tacitern/DigitalFadingLED/hardware/LedBoard/LedBoard.step

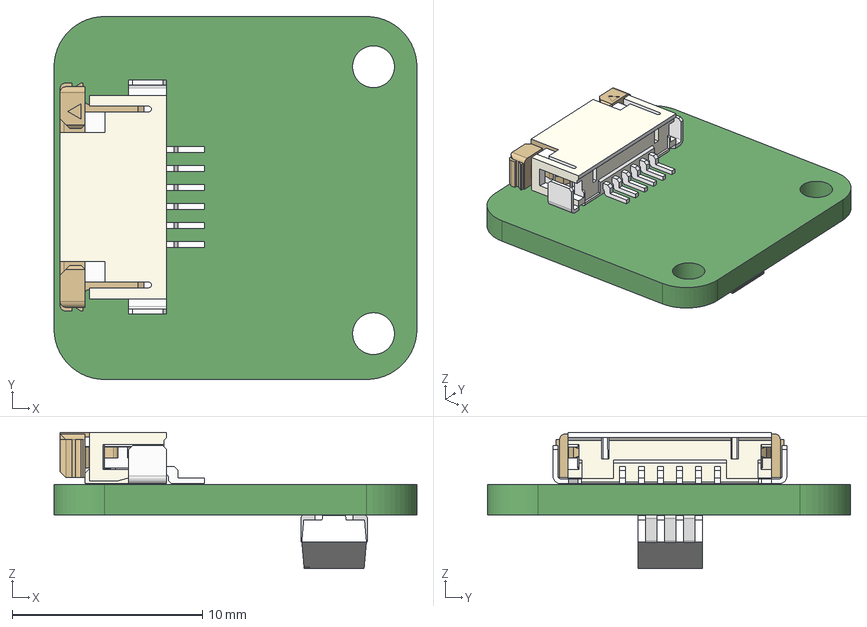
[picture p15: CAD file, 2021-11-26]
hardware/LedBoard/LedBoard.step
19.1 x 19.1 x 7.17 mm
