tacitern/DigitalFadingLED/hardware/ProgrammingAdapterBoard/footprints/Preci-Dip_851-87-007-20-001101_7pos_Soccket/851-87-007-20-001101.step

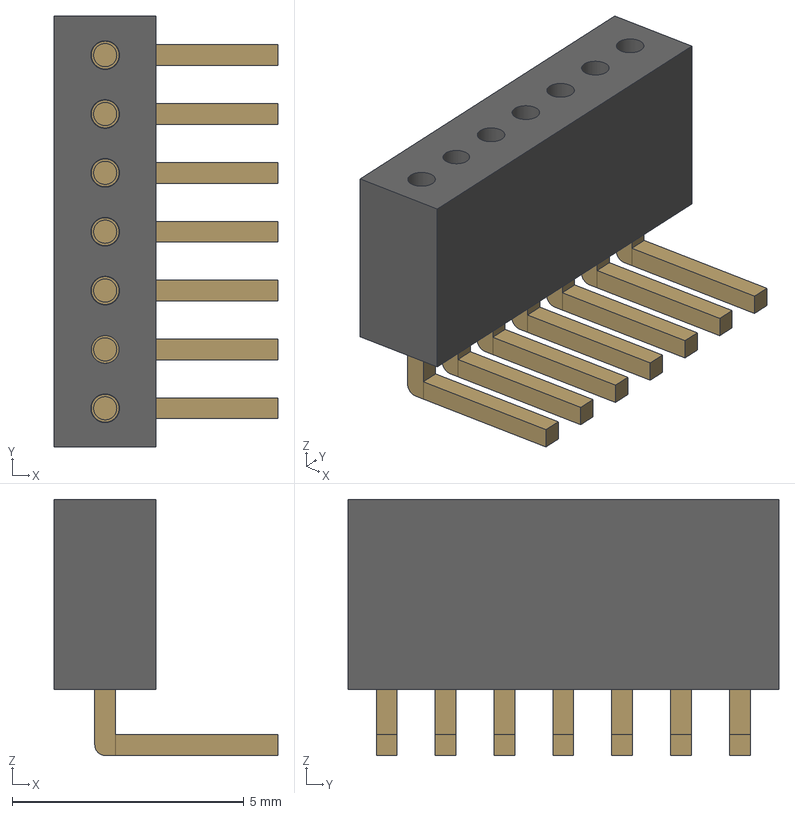
[picture p16: CAD file, 2021-11-26]
hardware/ProgrammingAdapterBoard/footprints/Preci-Dip_851-87-007-20-001101_7pos_Soccket/851-87-007-20-001101.step
4.83 x 9.30 x 5.52 mm
