tacitern/DigitalFadingLED/hardware/ProgrammingAdapterBoard/ProgrammingAdapterBoard.step

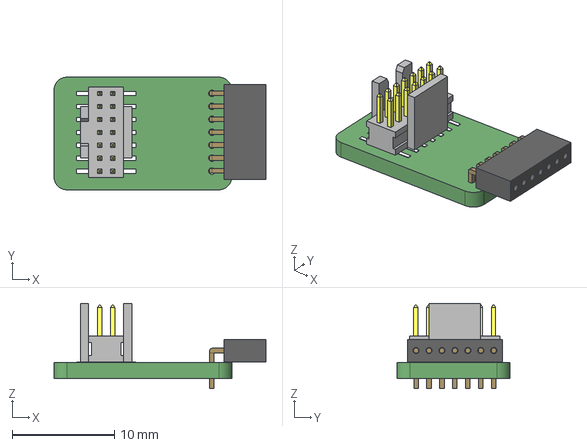
[picture p17: CAD file, 2021-11-26]
hardware/ProgrammingAdapterBoard/ProgrammingAdapterBoard.step
20.8 x 11.0 x 8.34 mm
