tacitern/DigitalFadingLED/hardware/DigitalFadingLED/footprints/FT230XS/FX230XS.FCStd

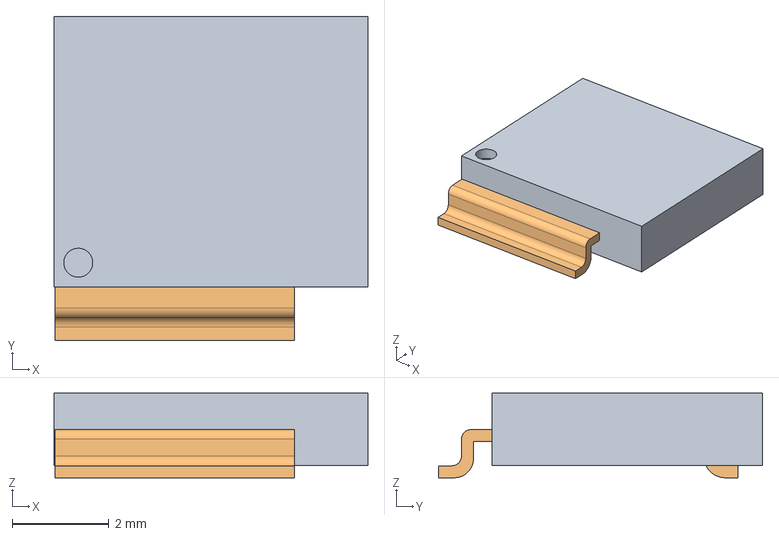
[picture p18: CAD file, 2021-11-26]
hardware/DigitalFadingLED/footprints/FT230XS/FX230XS.FCStd
6.50 x 6.71 x 1.75 mm
