tacitern/DigitalFadingLED/hardware/LedBoard/footprints/PLCC6.FCStd

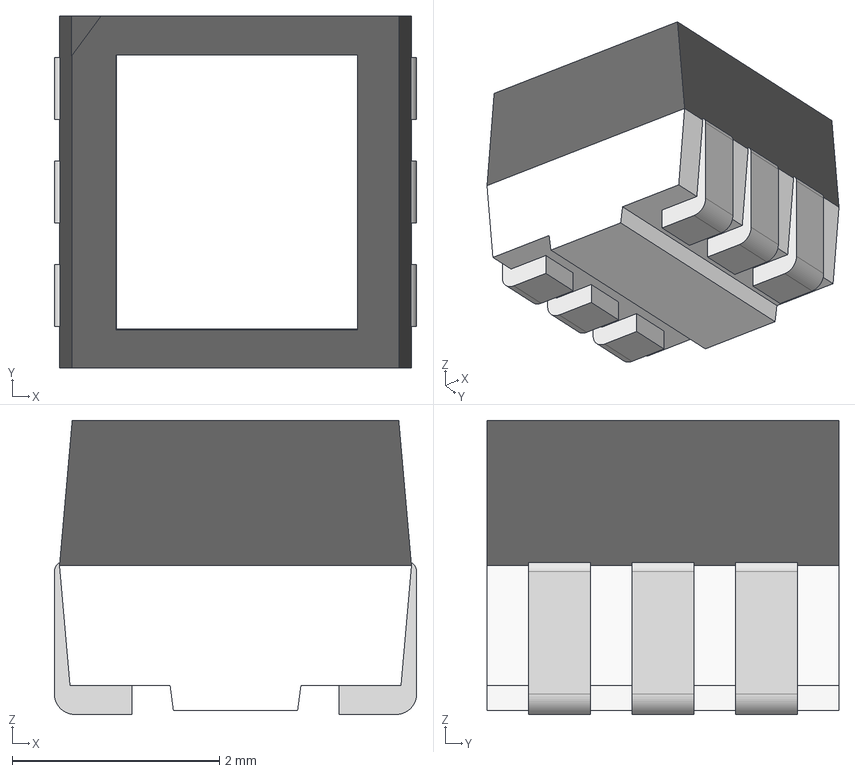
[picture p19: CAD file, 2021-11-26]
hardware/LedBoard/footprints/PLCC6.FCStd
3.50 x 3.40 x 2.84 mm
