tacitern/DigitalFadingLED/software/STM32F4DISCOVERY_DEV/DigitalFadingLED/Core/Src/tim.c

/**
  ******************************************************************************
  * @file    tim.c
  * @brief   This file provides code for the configuration
  *          of the TIM instances.
  ******************************************************************************
  * @attention
  *
  * <h2><center>&copy; Copyright (c) 2021 STMicroelectronics.
  * All rights reserved.</center></h2>
  *
  * This software component is licensed by ST under BSD 3-Clause license,
  * the "License"; You may not use this file except in compliance with the
  * License. You may obtain a copy of the License at:
  *                        opensource.org/licenses/BSD-3-Clause
  *
  ******************************************************************************
  */

/* Includes ------------------------------------------------------------------*/
#include "tim.h"

/* USER CODE BEGIN 0 */
void GetColorValues(uint8_t* colors){
  colors[0] = (uint8_t)htim4.Instance->CCR1;
  colors[1] = (uint8_t)htim4.Instance->CCR2;
  colors[2] = (uint8_t)htim4.Instance->CCR3;
}

void SetColorValues(uint8_t* colors){
  htim4.Instance->CCR1 = (uint32_t)colors[0];
  htim4.Instance->CCR2 = (uint32_t)colors[1];
  htim4.Instance->CCR3 = (uint32_t)colors[2];
}

uint16_t GetLuminanceValue(void){
  return (uint16_t)htim3.Instance->CCR1;
}

void SetLuminanceValue(uint16_t lum){
  htim3.Instance->CCR1 = (uint32_t)lum;
}

uint16_t rate = 0;
uint16_t GetRateValue(void){
  return rate;
}

void SetRateValue(uint16_t val){
  rate = val;
}

uint8_t time_flag = 0;
uint8_t dir = 0;
void ProcessLuminance(void){
  if(time_flag){
    if(dir == 0){
      htim3.Instance->CCR1 = htim3.Instance->CCR1 + rate;
    }
    else{
      htim3.Instance->CCR1 = htim3.Instance->CCR1 - rate;
    }
    if(dir == 0 && htim3.Instance->CCR1 > 1000){
      dir = 1;
    }
    else if(dir == 1 && htim3.Instance->CCR1 < rate){
      dir = 0;
    }

    time_flag = 0;
  }

}

void HAL_TIM_PeriodElapsedCallback(TIM_HandleTypeDef *htim){

  if (htim == &htim7){
    time_flag = 1;
  }
}
/* USER CODE END 0 */

TIM_HandleTypeDef htim3;
TIM_HandleTypeDef htim4;
TIM_HandleTypeDef htim7;

/* TIM3 init function */
void MX_TIM3_Init(void)
{

  TIM_MasterConfigTypeDef sMasterConfig = {0};
  TIM_OC_InitTypeDef sConfigOC = {0};

  htim3.Instance = TIM3;
  htim3.Init.Prescaler = 0;
  htim3.Init.CounterMode = TIM_COUNTERMODE_UP;
  htim3.Init.Period = 1000;
  htim3.Init.ClockDivision = TIM_CLOCKDIVISION_DIV1;
  htim3.Init.AutoReloadPreload = TIM_AUTORELOAD_PRELOAD_DISABLE;
  if (HAL_TIM_PWM_Init(&htim3) != HAL_OK)
  {
    Error_Handler();
  }
  sMasterConfig.MasterOutputTrigger = TIM_TRGO_RESET;
  sMasterConfig.MasterSlaveMode = TIM_MASTERSLAVEMODE_DISABLE;
  if (HAL_TIMEx_MasterConfigSynchronization(&htim3, &sMasterConfig) != HAL_OK)
  {
    Error_Handler();
  }
  sConfigOC.OCMode = TIM_OCMODE_PWM1;
  sConfigOC.Pulse = 0;
  sConfigOC.OCPolarity = TIM_OCPOLARITY_HIGH;
  sConfigOC.OCFastMode = TIM_OCFAST_DISABLE;
  if (HAL_TIM_PWM_ConfigChannel(&htim3, &sConfigOC, TIM_CHANNEL_1) != HAL_OK)
  {
    Error_Handler();
  }
  HAL_TIM_MspPostInit(&htim3);

}
/* TIM4 init function */
void MX_TIM4_Init(void)
{

  TIM_MasterConfigTypeDef sMasterConfig = {0};
  TIM_OC_InitTypeDef sConfigOC = {0};

  htim4.Instance = TIM4;
  htim4.Init.Prescaler = 49;
  htim4.Init.CounterMode = TIM_COUNTERMODE_UP;
  htim4.Init.Period = 255;
  htim4.Init.ClockDivision = TIM_CLOCKDIVISION_DIV1;
  htim4.Init.AutoReloadPreload = TIM_AUTORELOAD_PRELOAD_DISABLE;
  if (HAL_TIM_PWM_Init(&htim4) != HAL_OK)
  {
    Error_Handler();
  }
  sMasterConfig.MasterOutputTrigger = TIM_TRGO_RESET;
  sMasterConfig.MasterSlaveMode = TIM_MASTERSLAVEMODE_DISABLE;
  if (HAL_TIMEx_MasterConfigSynchronization(&htim4, &sMasterConfig) != HAL_OK)
  {
    Error_Handler();
  }
  sConfigOC.OCMode = TIM_OCMODE_PWM1;
  sConfigOC.Pulse = 0;
  sConfigOC.OCPolarity = TIM_OCPOLARITY_HIGH;
  sConfigOC.OCFastMode = TIM_OCFAST_DISABLE;
  if (HAL_TIM_PWM_ConfigChannel(&htim4, &sConfigOC, TIM_CHANNEL_1) != HAL_OK)
  {
    Error_Handler();
  }
  if (HAL_TIM_PWM_ConfigChannel(&htim4, &sConfigOC, TIM_CHANNEL_2) != HAL_OK)
  {
    Error_Handler();
  }
  if (HAL_TIM_PWM_ConfigChannel(&htim4, &sConfigOC, TIM_CHANNEL_3) != HAL_OK)
  {
    Error_Handler();
  }
  HAL_TIM_MspPostInit(&htim4);

}
/* TIM7 init function */
void MX_TIM7_Init(void)
{

  TIM_MasterConfigTypeDef sMasterConfig = {0};

  htim7.Instance = TIM7;
  htim7.Init.Prescaler = 19;
  htim7.Init.CounterMode = TIM_COUNTERMODE_UP;
  htim7.Init.Period = 25000;
  htim7.Init.AutoReloadPreload = TIM_AUTORELOAD_PRELOAD_DISABLE;
  if (HAL_TIM_Base_Init(&htim7) != HAL_OK)
  {
    Error_Handler();
  }
  sMasterConfig.MasterOutputTrigger = TIM_TRGO_RESET;
  sMasterConfig.MasterSlaveMode = TIM_MASTERSLAVEMODE_DISABLE;
  if (HAL_TIMEx_MasterConfigSynchronization(&htim7, &sMasterConfig) != HAL_OK)
  {
    Error_Handler();
  }
}

void HAL_TIM_PWM_MspInit(TIM_HandleTypeDef* tim_pwmHandle)
{

  if(tim_pwmHandle->Instance==TIM3)
  {
    /* TIM3 clock enable */
    __HAL_RCC_TIM3_CLK_ENABLE();
  }
  else if(tim_pwmHandle->Instance==TIM4)
  {
    /* TIM4 clock enable */
    __HAL_RCC_TIM4_CLK_ENABLE();
  }
}

void HAL_TIM_Base_MspInit(TIM_HandleTypeDef* tim_baseHandle)
{

  if(tim_baseHandle->Instance==TIM7)
  {
    /* TIM7 clock enable */
    __HAL_RCC_TIM7_CLK_ENABLE();

    /* TIM7 interrupt Init */
    HAL_NVIC_SetPriority(TIM7_IRQn, 0, 0);
    HAL_NVIC_EnableIRQ(TIM7_IRQn);
  }
}
void HAL_TIM_MspPostInit(TIM_HandleTypeDef* timHandle)
{

  GPIO_InitTypeDef GPIO_InitStruct = {0};
  if(timHandle->Instance==TIM3)
  {
    __HAL_RCC_GPIOC_CLK_ENABLE();
    /**TIM3 GPIO Configuration
    PC6     ------> TIM3_CH1
    */
    GPIO_InitStruct.Pin = GPIO_PIN_6;
    GPIO_InitStruct.Mode = GPIO_MODE_AF_OD;
    GPIO_InitStruct.Pull = GPIO_NOPULL;
    GPIO_InitStruct.Speed = GPIO_SPEED_FREQ_HIGH;
    GPIO_InitStruct.Alternate = GPIO_AF2_TIM3;
    HAL_GPIO_Init(GPIOC, &GPIO_InitStruct);

  }
  else if(timHandle->Instance==TIM4)
  {
    __HAL_RCC_GPIOD_CLK_ENABLE();
    /**TIM4 GPIO Configuration
    PD12     ------> TIM4_CH1
    PD13     ------> TIM4_CH2
    PD14     ------> TIM4_CH3
    */
    GPIO_InitStruct.Pin = GPIO_PIN_12|GPIO_PIN_13|GPIO_PIN_14;
    GPIO_InitStruct.Mode = GPIO_MODE_AF_PP;
    GPIO_InitStruct.Pull = GPIO_NOPULL;
    GPIO_InitStruct.Speed = GPIO_SPEED_FREQ_HIGH;
    GPIO_InitStruct.Alternate = GPIO_AF2_TIM4;
    HAL_GPIO_Init(GPIOD, &GPIO_InitStruct);

  }

}

void HAL_TIM_PWM_MspDeInit(TIM_HandleTypeDef* tim_pwmHandle)
{

  if(tim_pwmHandle->Instance==TIM3)
  {
    /* Peripheral clock disable */
    __HAL_RCC_TIM3_CLK_DISABLE();
  }
  else if(tim_pwmHandle->Instance==TIM4)
  {
    /* Peripheral clock disable */
    __HAL_RCC_TIM4_CLK_DISABLE();
  }
}

void HAL_TIM_Base_MspDeInit(TIM_HandleTypeDef* tim_baseHandle)
{

  if(tim_baseHandle->Instance==TIM7)
  {
    /* Peripheral clock disable */
    __HAL_RCC_TIM7_CLK_DISABLE();

    /* TIM7 interrupt Deinit */
    HAL_NVIC_DisableIRQ(TIM7_IRQn);
  }
}

/************************ (C) COPYRIGHT STMicroelectronics *****END OF FILE****/
